crides/steno/compiler/src/stroke.rs

//! Stroke parsing and displaying utilities
use std::fmt::{self, Debug, Display, Formatter};
use std::str::FromStr;

use crate::hash;

pub static KEYS: &str = "#STKPWHRAO*EUFRPBLGTSDZ";

#[derive(PartialEq, Eq, Hash, PartialOrd, Ord, Clone, Copy)]
pub struct Stroke(pub u32);

impl Stroke {
    pub fn new() -> Self {
        Self(0)
    }

    pub fn set(&mut self, bit: usize) {
        self.0 |= 1 << bit;
    }

    pub fn is_set(&self, bit: usize) -> bool {
        self.0 & (1 << bit) != 0
    }

    pub fn raw(self) -> u32 {
        self.0
    }

    /// From FNV-1a
    pub fn hash(self, init: Option<u32>) -> u32 {
        let bytes = self.0.to_le_bytes();
        hash::hash(&bytes, init)
    }
}

pub fn hash_strokes(strokes: &Strokes) -> u32 {
    let mut hash = None;
    for stroke in &strokes.0 {
        hash = Some(stroke.hash(hash));
    }
    hash.unwrap()
}

impl Display for Stroke {
    fn fmt(&self, f: &mut Formatter) -> fmt::Result {
        const DIGIT_BITS: u32 = 0x7562A8;
        static KEYS: &str = "#STKPWHRAO*EUFRPBLGTSDZ";
        let mut buf = String::new();
        if self.is_set(22) && (self.0 & !DIGIT_BITS) != 0 {
            for &(bit, digit) in &[
                (21, '1'),
                (20, '2'),
                (18, '3'),
                (16, '4'),
                (14, '5'),
                (13, '0'),
                (9, '6'),
                (7, '7'),
                (5, '8'),
                (3, '9'),
            ] {
                if self.is_set(bit) {
                    buf.push(digit);
                }
            }
        } else {
            let mut has_mid = false;
            for i in (0..23).rev() {
                if (self.0 & (1 << i)) > 0 {
                    if i < 10 {
                        if !has_mid {
                            buf.push('-');
                            has_mid = true;
                        }
                    } else if i <= 14 {
                        has_mid = true;
                    }
                    buf.push(KEYS.chars().nth(22 - i).unwrap());
                }
            }
        }
        write!(f, "{}", buf)
    }
}

#[derive(Debug, Clone, PartialEq, Eq, PartialOrd, Ord)]
pub struct Strokes(pub Vec<Stroke>);

impl Strokes {
    pub fn len(&self) -> usize {
        self.0.len()
    }
}

impl Display for Strokes {
    fn fmt(&self, f: &mut Formatter) -> fmt::Result {
        let strs = self.0.iter().map(|s| format!("{}", s)).collect::<Vec<_>>();
        write!(f, "{}", strs.join("/"))
    }
}

impl Debug for Stroke {
    fn fmt(&self, f: &mut Formatter) -> fmt::Result {
        f.debug_tuple("Stroke")
            .field(&format_args!("{:06x}", &self.0))
            .field(&format_args!("{}", &self))
            .finish()
    }
}

#[derive(Debug)]
pub struct StrokeParseError(String, char);

impl Display for StrokeParseError {
    fn fmt(&self, f: &mut Formatter) -> fmt::Result {
        write!(f, "Unknown char '{}' in string '{}'", self.1, self.0)
    }
}

impl FromStr for Stroke {
    type Err = StrokeParseError;
    fn from_str(s: &str) -> Result<Self, Self::Err> {
        let mut res = Stroke::new();
        let mut ind = 0;
        for c in s.chars() {
            match c {
                dig @ '0'..='9' => {
                    res.set(KEYS.len() - 1);
                    let mapped = match dig {
                        '1' => 21,
                        '2' => 20,
                        '3' => 18,
                        '4' => 16,
                        '5' => 14,
                        '0' => 13,
                        '6' => 9,
                        '7' => 7,
                        '8' => 5,
                        '9' => 3,
                        _ => panic!(),
                    };
                    res.set(mapped);
                }
                '-' => ind = KEYS.find('*').unwrap(),
                '#' => res.set(KEYS.len() - 1),
                _ => {
                    ind += KEYS[ind..]
                        .find(c)
                        .ok_or_else(|| StrokeParseError(s.to_string(), c))?;
                    res.set(KEYS.len() - ind - 1);
                }
            }
        }
        Ok(res)
    }
}
